berauser/loololu/documenation/pictures/loolou_001.jpg

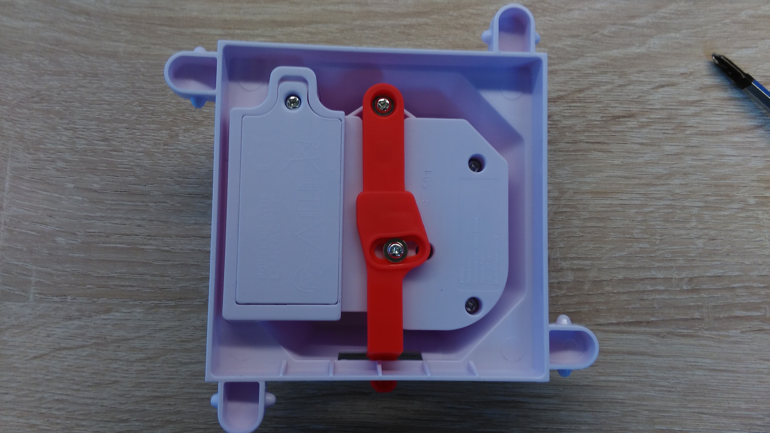
documenation/pictures/loolou_001.jpg
